ysfkm/Power_Supply/OscilloscopeSnapshotTool/Snapshots/v0.1_+5V_20260813_134420/longcapture_20260813_134420/snapshot_20260813_134420_LONG.png

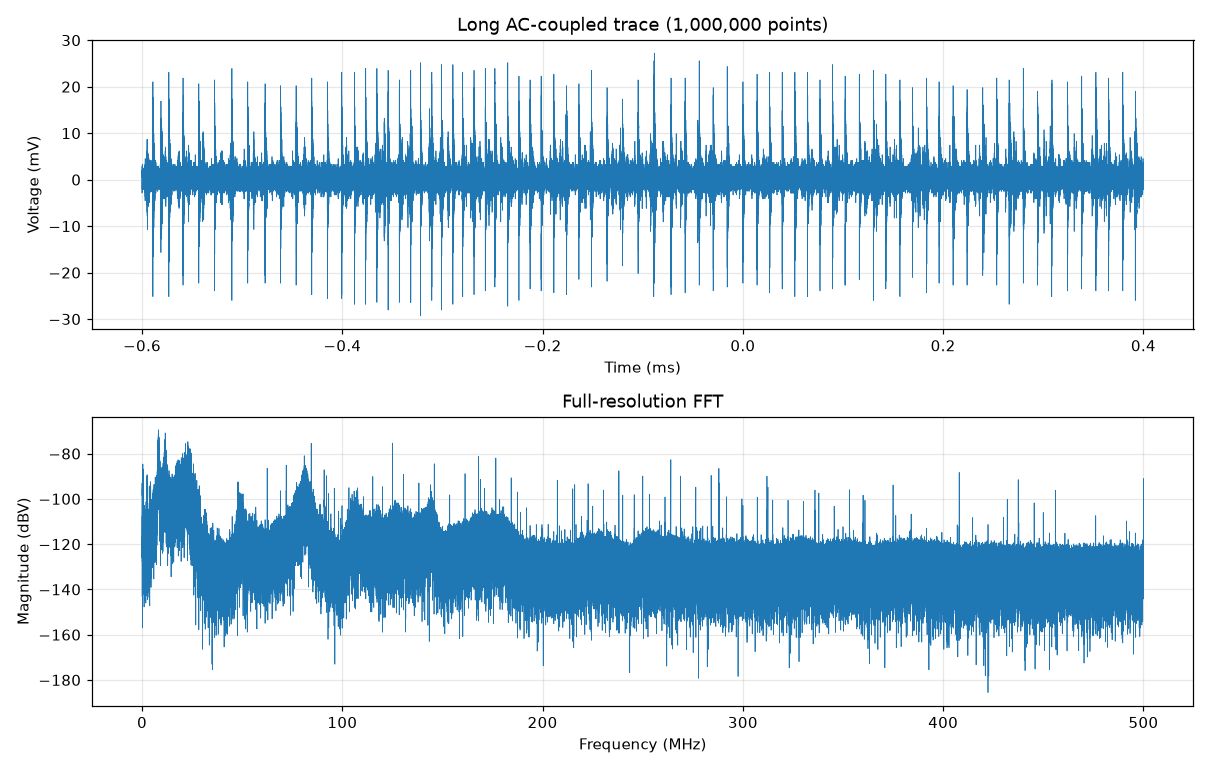
OscilloscopeSnapshotTool/Snapshots/v0.1_+5V_20260813_134420/longcapture_20260813_134420/snapshot_20260813_134420_LONG.png
